christm45/eyepiece-4-achromats/base basse cavité lentilles 40mm coté focuser 2 inch_2.png

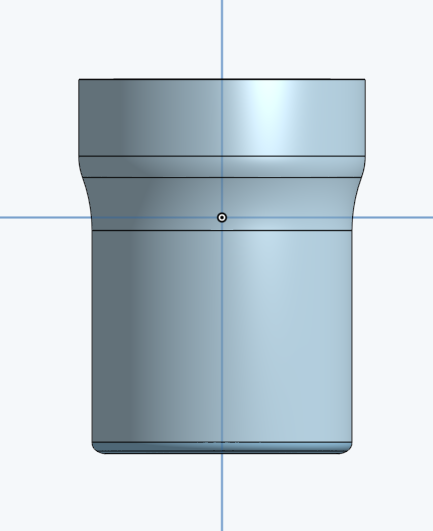
base basse cavité lentilles 40mm coté focuser 2 inch_2.png
