christm45/eyepiece-4-achromats/top eye piece acceuil lentilles 30mm_2.png

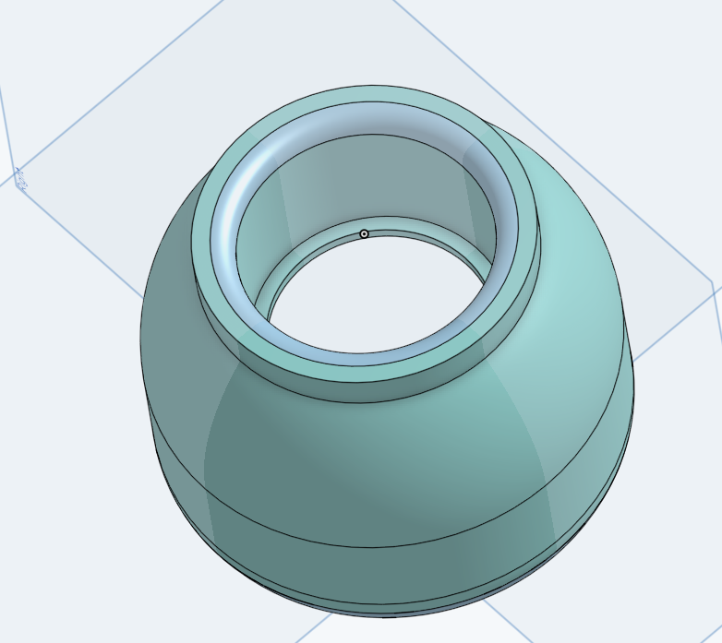
top eye piece acceuil lentilles 30mm_2.png
