christm45/eyepiece-4-achromats/top eye piece acceuil lentilles 30mm_mesures.png

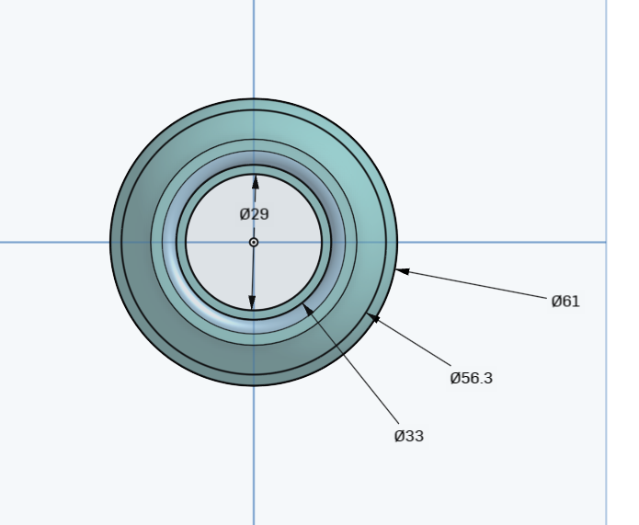
top eye piece acceuil lentilles 30mm_mesures.png
