christm45/eyepiece-4-achromats/top ring eye side.png

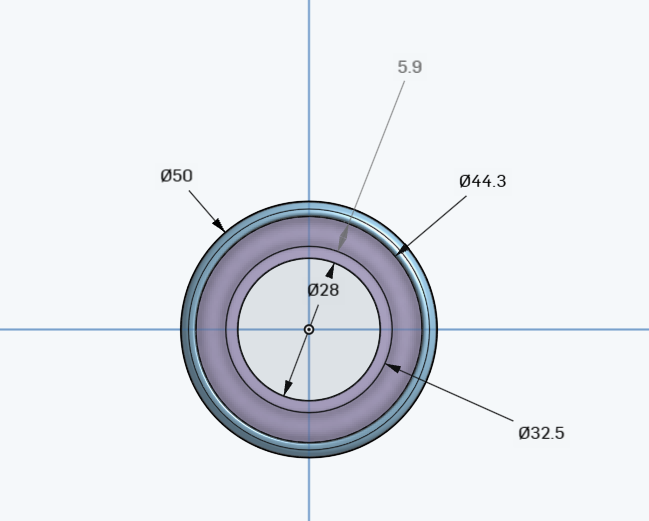
top ring eye side.png
