christm45/eyepiece-4-achromats/banc focale lentilles/5_support_source.stl

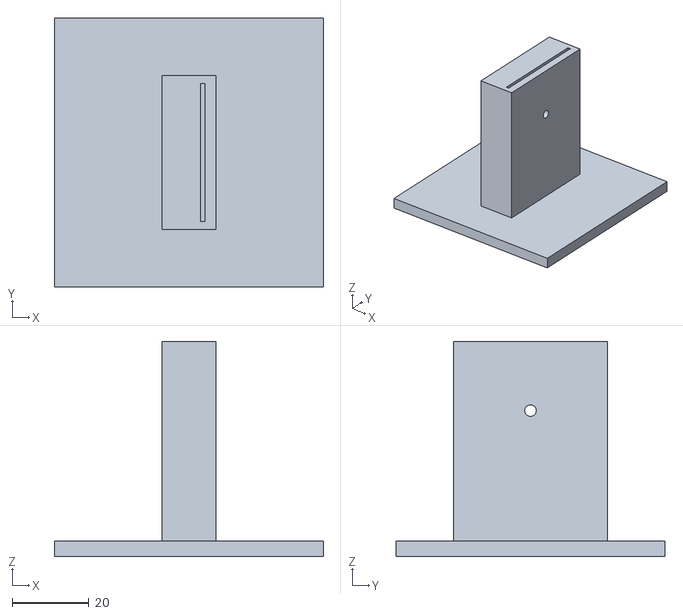
[picture p25: CAD file, 2026-10-08]
banc focale lentilles/5_support_source.stl
70.0 x 70.0 x 56.0
