christm45/eyepiece-4-achromats/stl_oculaire/3_coiffe_oeil_poche_D33.stl

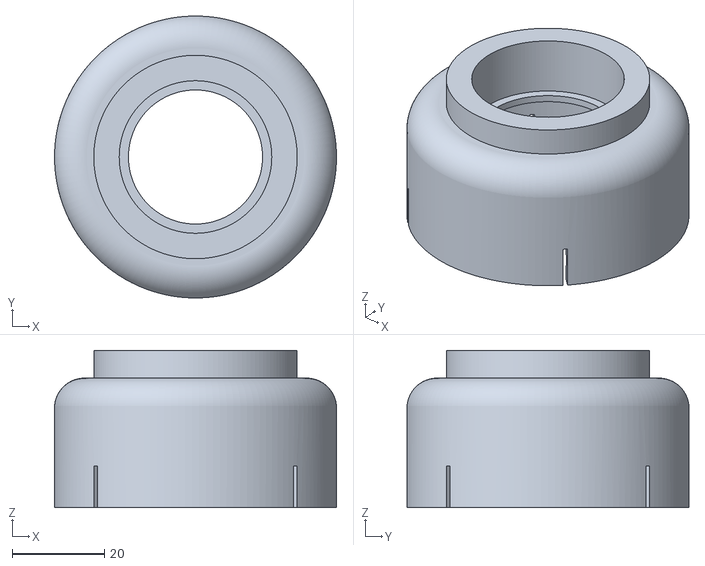
[picture p26: CAD file, 2026-10-08]
stl_oculaire/3_coiffe_oeil_poche_D33.stl
61.0 x 61.0 x 34.0
