christm45/eyepiece-4-achromats/assemblage occulaire 30mm.png

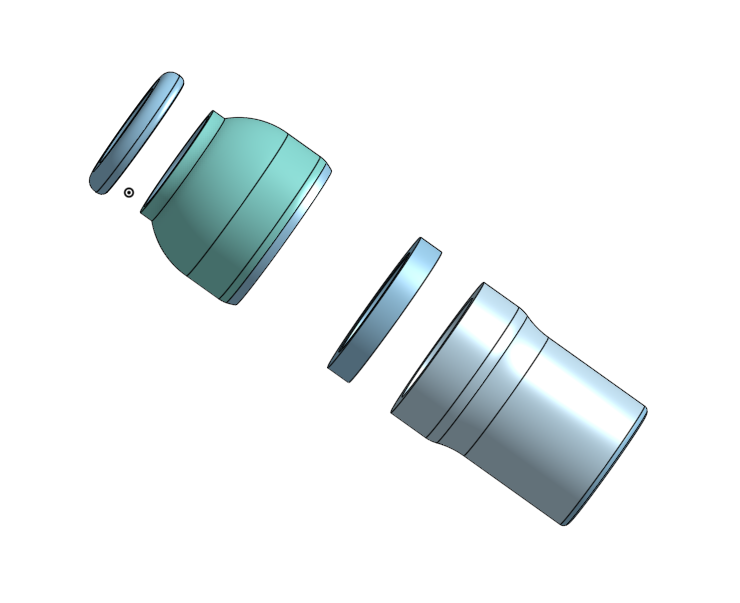
assemblage occulaire 30mm.png
